jkrame1/SAIC-Converter/Hardware/Between Build v1.1.0 - 94.jpg

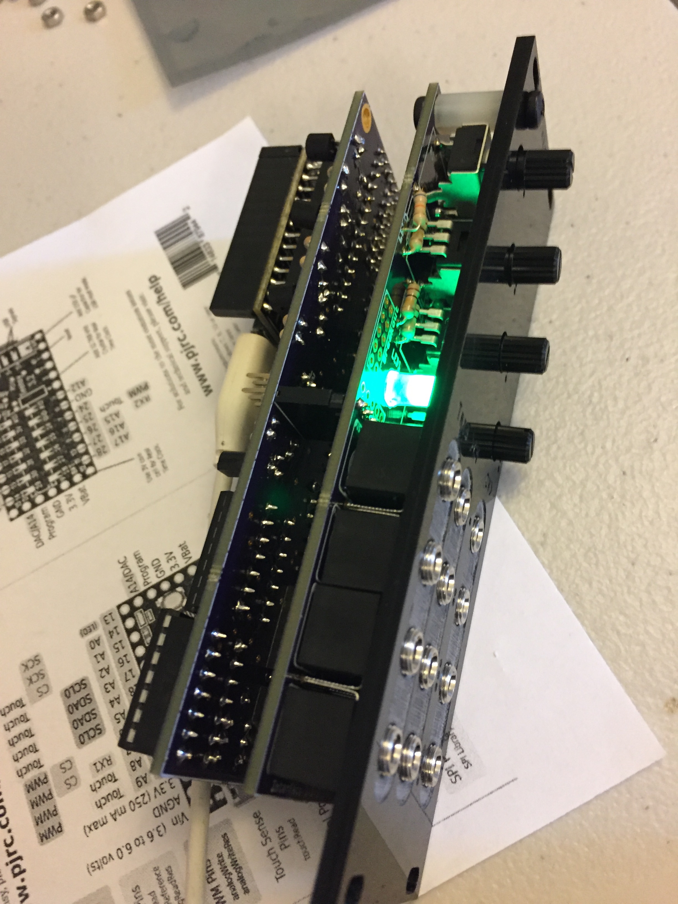
Hardware/Between Build v1.1.0 - 94.jpg
