jkrame1/SAIC-Converter/Hardware/Gallery/Austin Gladney 2.JPG

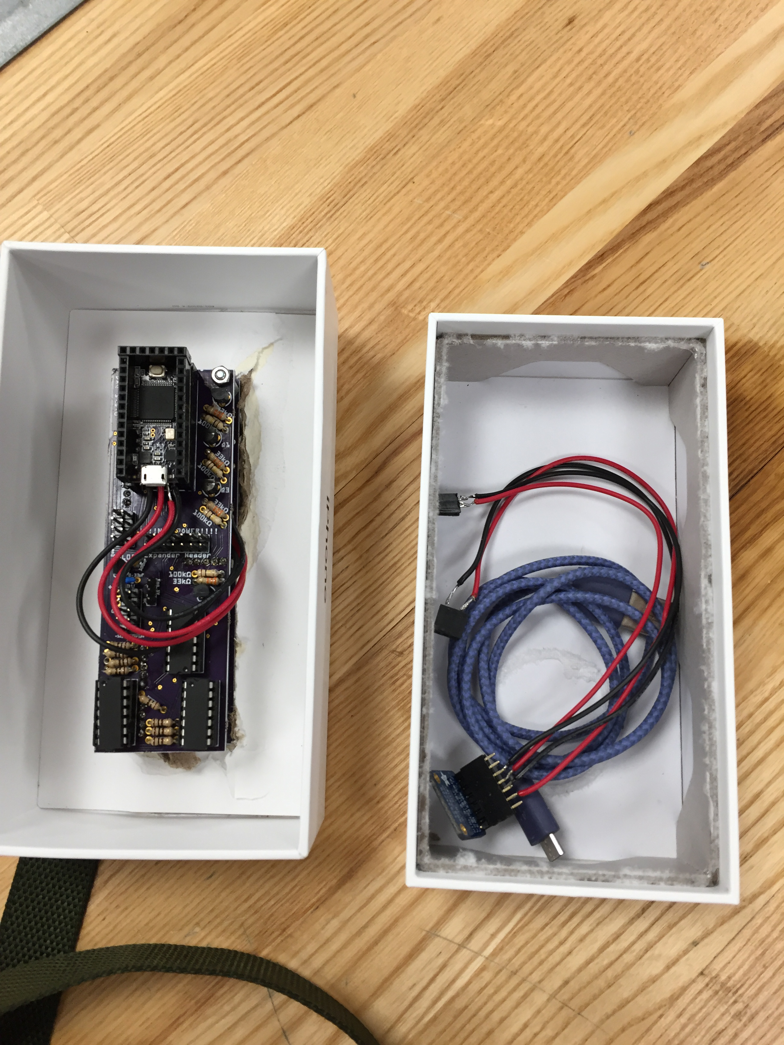
Hardware/Gallery/Austin Gladney 2.JPG
