jkrame1/SAIC-Converter/Hardware/Gallery/Austin Gladney 1.JPG

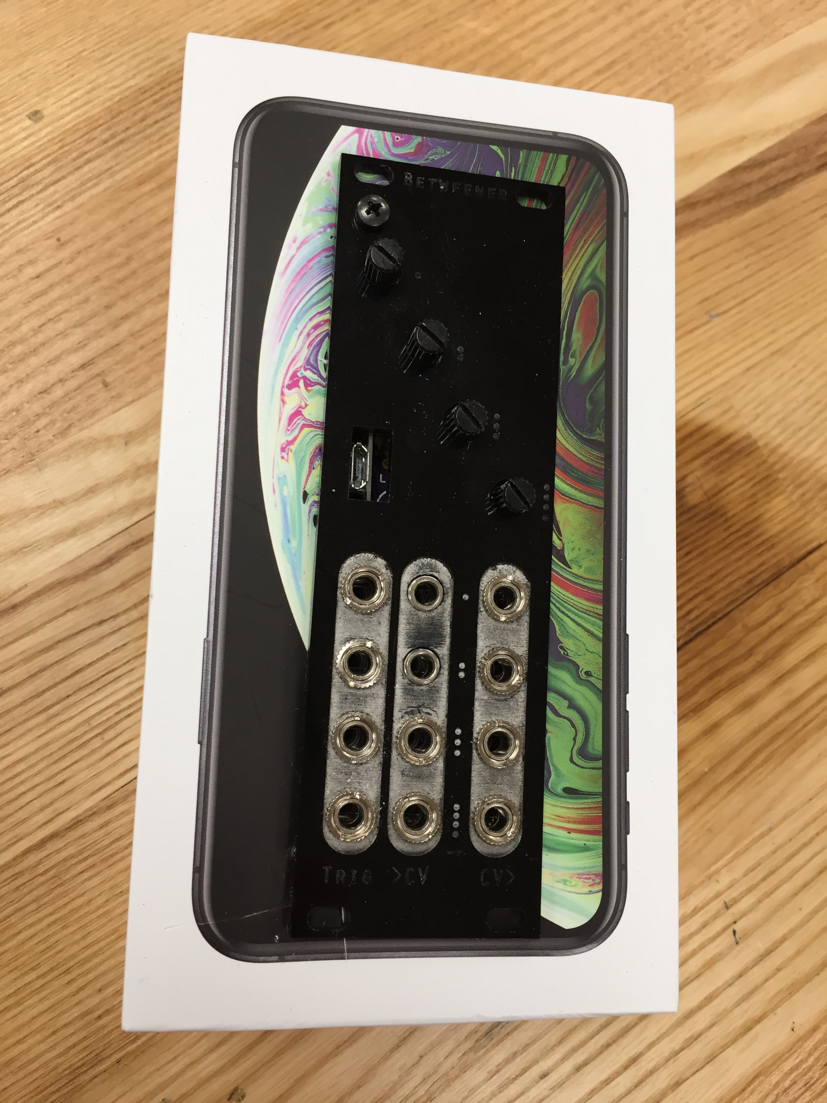
Hardware/Gallery/Austin Gladney 1.JPG
